jonno-l-r/networked_weather_station/docs/media/layout_screenshot.png

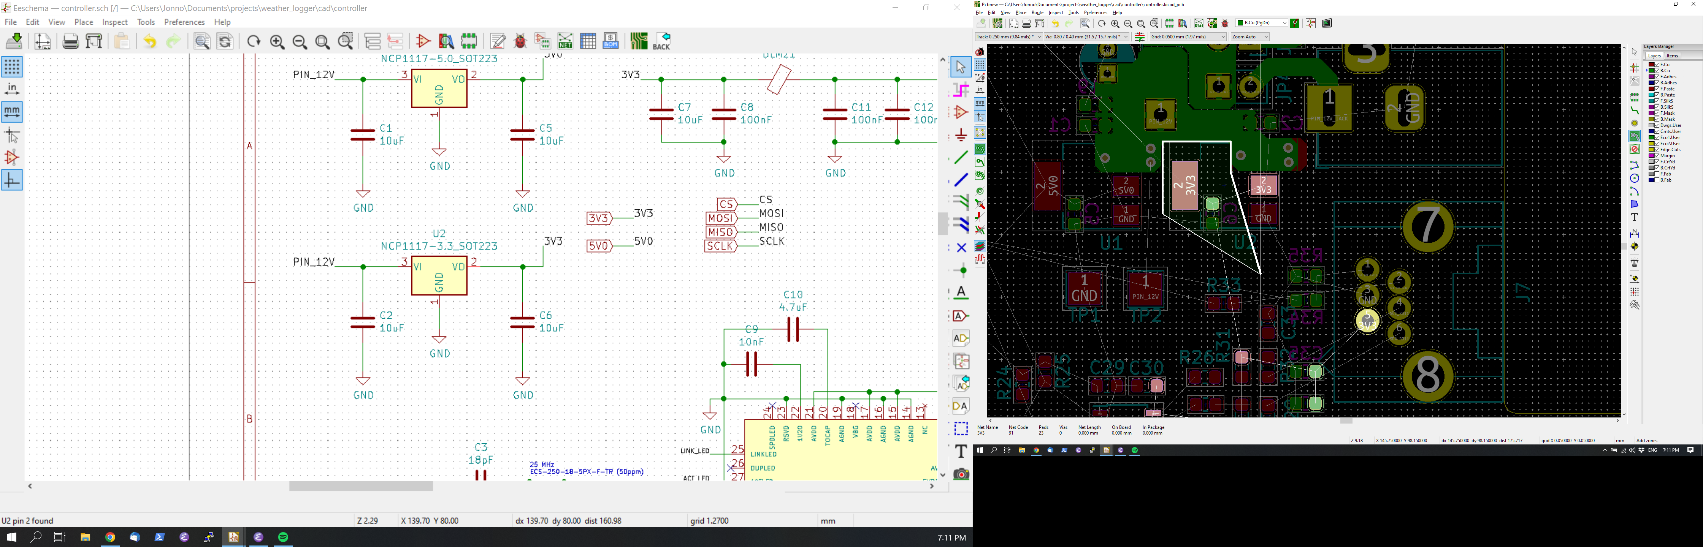
docs/media/layout_screenshot.png
