jonno-l-r/networked_weather_station/docs/media/photos/IMG_0136.JPG

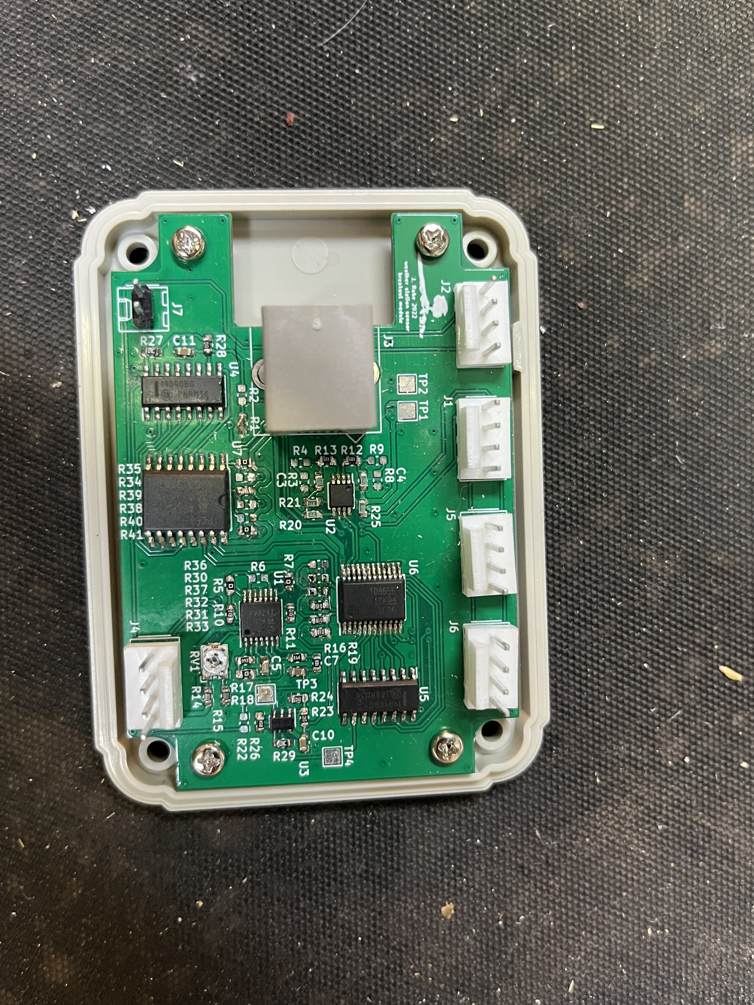
docs/media/photos/IMG_0136.JPG
